vazhnov/HydraMeter_0.4/MMTR_AFE_00_04_TORELEASE/Schematic_PDF_and_Pics/Ohm_AFE.png

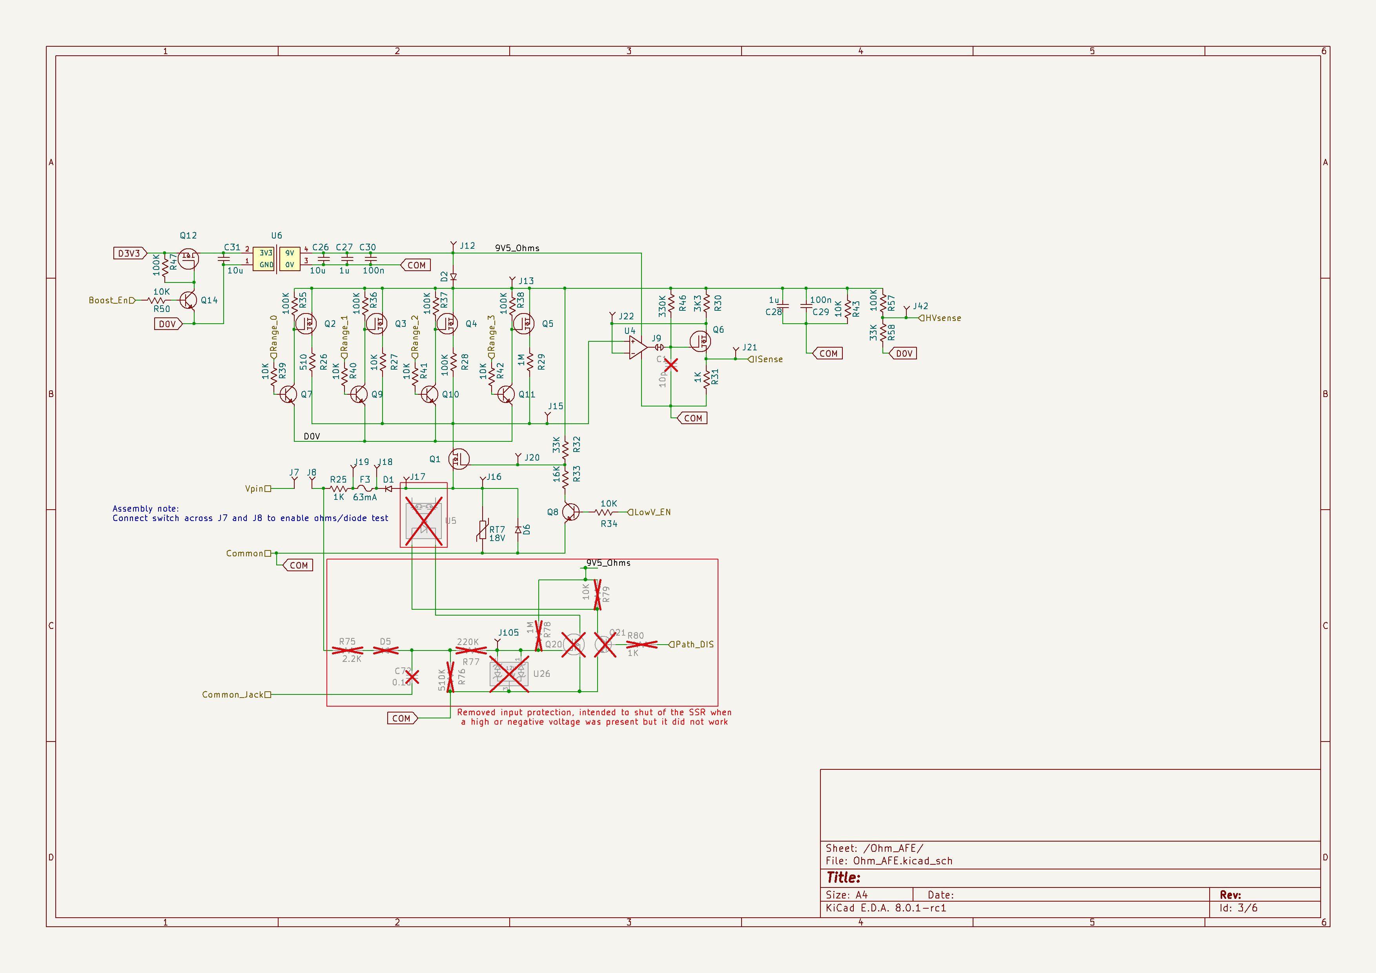
MMTR_AFE_00_04_TORELEASE/Schematic_PDF_and_Pics/Ohm_AFE.png
