vazhnov/HydraMeter_0.4/MMTR_AFE_00_04_TORELEASE/Schematic_PDF_and_Pics/PGA_ADC.png

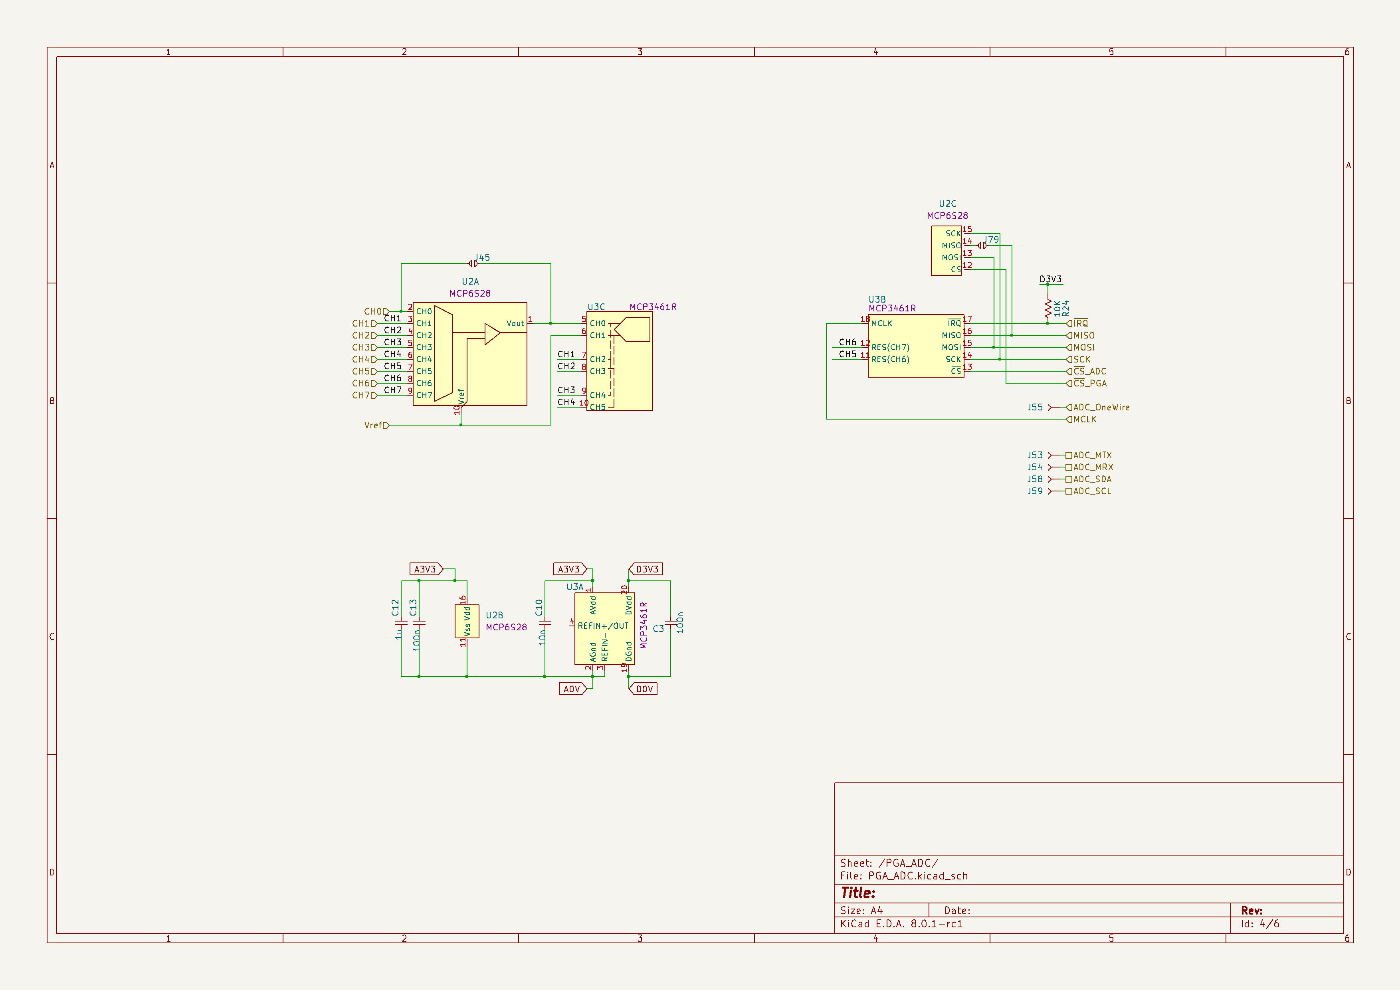
MMTR_AFE_00_04_TORELEASE/Schematic_PDF_and_Pics/PGA_ADC.png
