vazhnov/HydraMeter_0.4/MMTR_V00_03_Case/raspberry-pi-pico-r3-1.snapshot.2/SMD Resistor, Configurable, Raspberry Pi Pico-R3.SLDPRT

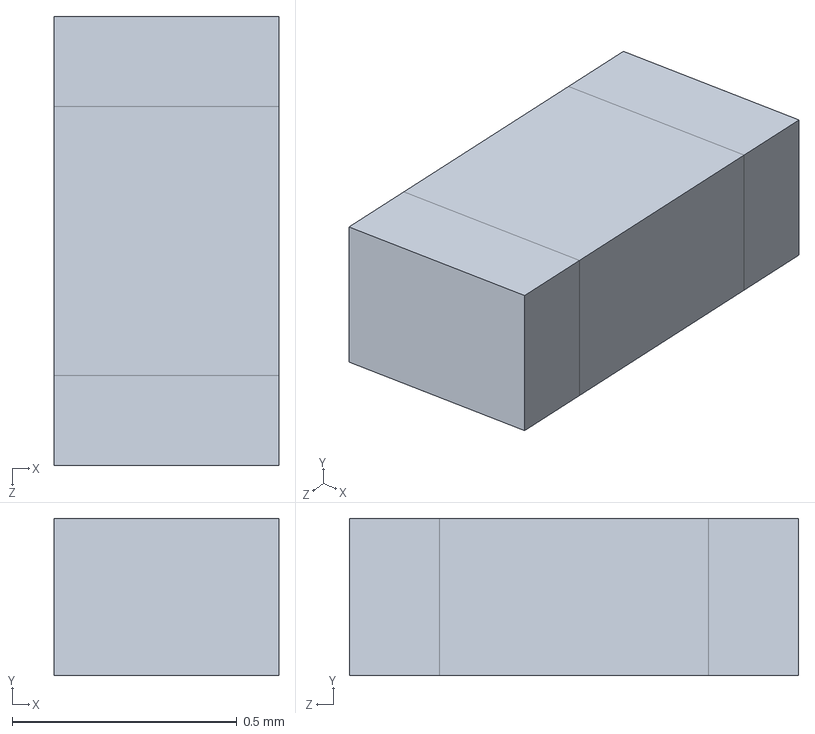
[picture p21: CAD file, 2024-12-21]
MMTR_V00_03_Case/raspberry-pi-pico-r3-1.snapshot.2/SMD Resistor, Configurable, Raspberry Pi Pico-R3.SLDPRT
0.5 x 0.35 x 1.00 mm
