vazhnov/HydraMeter_0.4/MMTR_V00_03_Case/raspberry-pi-pico-r3-1.snapshot.2/MicroUSB Port, Raspberry Pi Pico-R3.SLDPRT

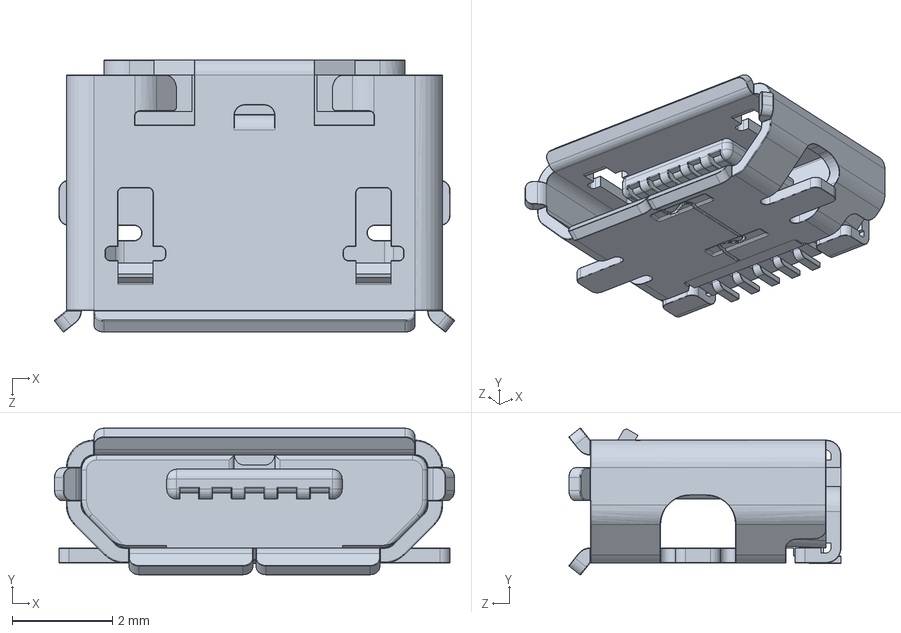
[picture p22: CAD file, 2024-12-21]
MMTR_V00_03_Case/raspberry-pi-pico-r3-1.snapshot.2/MicroUSB Port, Raspberry Pi Pico-R3.SLDPRT
7.97 x 2.92 x 5.43 mm
