vazhnov/HydraMeter_0.4/MMTR_V00_03_Case/raspberry-pi-pico-r3-1.snapshot.2/Q1, MOSFET, DMG1012T, Raspberry Pi Pico-R3.SLDPRT

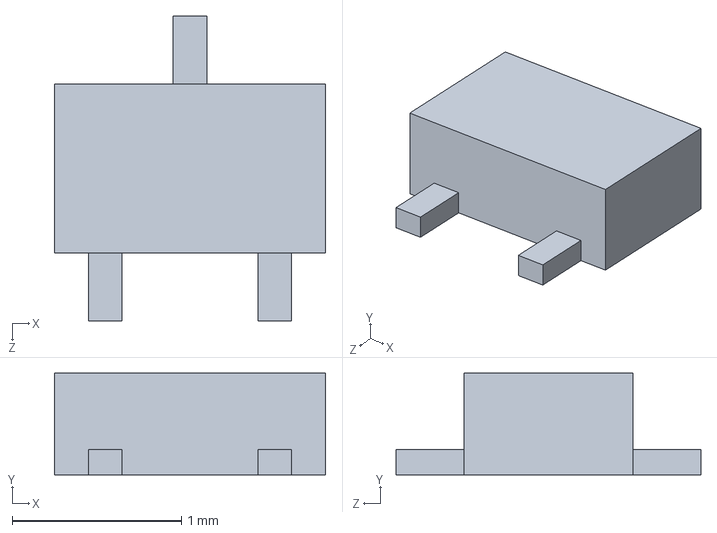
[picture p23: CAD file, 2024-12-21]
MMTR_V00_03_Case/raspberry-pi-pico-r3-1.snapshot.2/Q1, MOSFET, DMG1012T, Raspberry Pi Pico-R3.SLDPRT
1.60 x 0.6 x 1.80 mm
