vazhnov/HydraMeter_0.4/MMTR_V00_03_Case/raspberry-pi-pico-r3-1.snapshot.2/SW1, Tact Switch, Raspberry Pi Pico-R3.SLDPRT

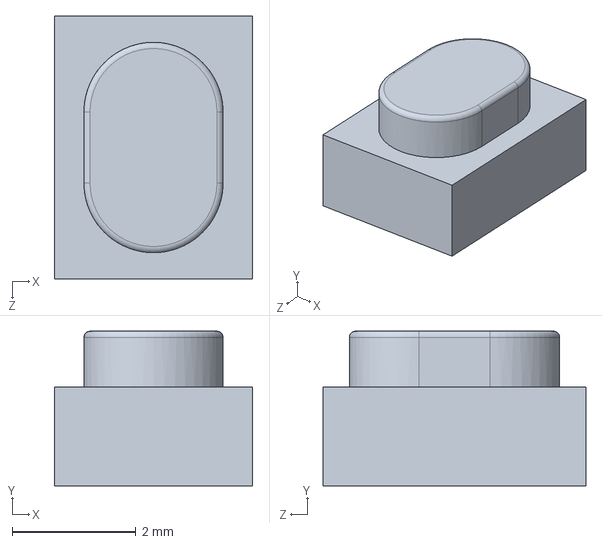
[picture p24: CAD file, 2024-12-21]
MMTR_V00_03_Case/raspberry-pi-pico-r3-1.snapshot.2/SW1, Tact Switch, Raspberry Pi Pico-R3.SLDPRT
3.20 x 2.50 x 4.25 mm
