vazhnov/HydraMeter_0.4/MMTR_V00_03_Case/raspberry-pi-pico-r3-1.snapshot.2/D2, QSME-C194, LED, Raspberry Pi Pico-R3.SLDPRT

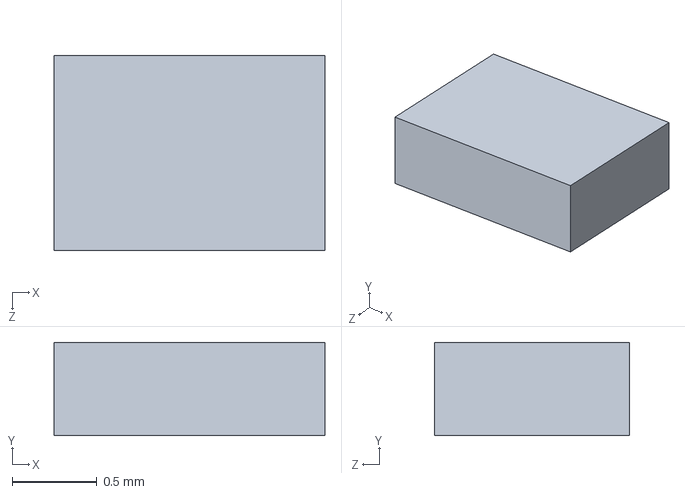
[picture p25: CAD file, 2024-12-21]
MMTR_V00_03_Case/raspberry-pi-pico-r3-1.snapshot.2/D2, QSME-C194, LED, Raspberry Pi Pico-R3.SLDPRT
1.60 x 0.55 x 1.15 mm
