vazhnov/HydraMeter_0.4/MMTR_V00_03_Case/raspberry-pi-pico-r3-1.snapshot.2/L1, Inductor, Raspberry Pi Pico-R3.SLDPRT

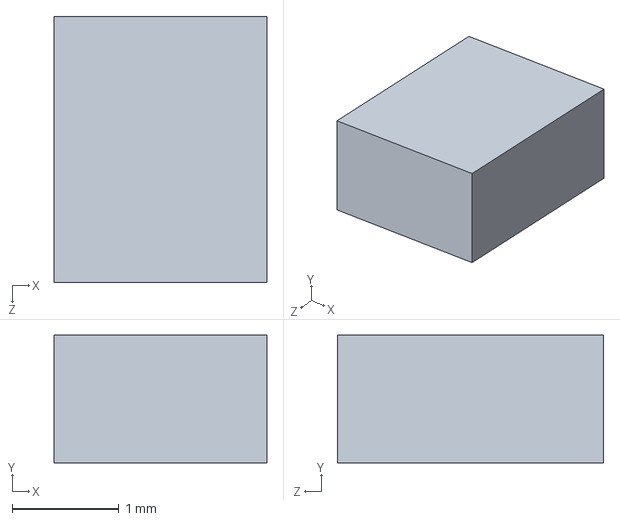
[picture p26: CAD file, 2024-12-21]
MMTR_V00_03_Case/raspberry-pi-pico-r3-1.snapshot.2/L1, Inductor, Raspberry Pi Pico-R3.SLDPRT
2.00 x 1.20 x 2.50 mm
