vazhnov/HydraMeter_0.4/Code/Display_VP_10_WirelessV2_SC/16ptFont_16_22_5_57.h

#ifndef FONT16_H
#define FONT16_H
uint8_t fontAsciiOffset_16 = 32;
uint8_t fontHtBytes_16 = 2;
uint8_t fontMaxWid_16 = 17;
int fontNumChars_16 = 98;
//uint8_t fontWidths[]
//int fontOffsets[]
uint8_t fontData_16[] = {
  0x00,0x00,0x00,0x00,0x00,0x00,0x00,0x00,   0x00,0x00,0x00,0x00,0x00,0x00,0x00,0x00,   // = 32 ==  
  0x00,0x00,0x7F,0x7F,0x00,0x00,   0x00,0x00,0xF3,0xF3,0x00,0x00,   // = 33 == !
  0x00,0x00,0x7C,0x7C,0x00,0x7C,0x7C,0x00,0x00,   0x00,0x00,0x00,0x00,0x00,0x00,0x00,0x00,0x00,   // = 34 == "
  0x00,0x00,0x06,0x06,0x07,0x7F,0x7E,0x06,0x06,0x07,0x7F,0x7E,0x06,0x06,   0x00,0x18,0x1B,0x7F,0xFC,0xD8,0x18,0x19,0x3F,0xFE,0xF8,0x18,0x18,0x00,   // = 35 == #
  0x00,0x1E,0x3F,0x33,0x61,0xFF,0xFF,0x70,0x3C,0x18,0x00,   0x00,0x0C,0x0E,0x87,0x83,0xFF,0xFF,0xE3,0x7F,0x3E,0x00,   // = 36 == $
  0x00,0x1F,0x3F,0x61,0x61,0x3F,0x3F,0x00,0x03,0x0F,0x3C,0x70,0x40,0x00,0x00,0x00,   0x00,0x00,0x80,0x80,0x83,0x8F,0x3C,0xF0,0xC0,0x3C,0x7E,0xC3,0xC3,0xC3,0x7E,0x3C,   // = 37 == %
  0x00,0x00,0x00,0x1E,0x3F,0x31,0x71,0x73,0x3F,0x3E,0x00,0x00,0x00,0x00,   0x00,0x3C,0x7E,0xE7,0xC3,0xE3,0xF3,0xBF,0x1E,0x1E,0x3F,0x73,0x01,0x00,   // = 38 == &
  0x00,0x00,0x7C,0x7C,0x00,0x00,   0x00,0x00,0x00,0x00,0x00,0x00,   // = 39 == '
  0x00,0x0F,0x3F,0xF0,0x80,0x80,   0x00,0xF0,0xFC,0x1E,0x03,0x00,   // = 40 == (
  0x00,0x80,0xC0,0xFC,0x3F,0x07,   0x00,0x01,0x03,0x3E,0xF8,0xE0,   // = 41 == )
  0x00,0x18,0x1A,0x7E,0x7C,0x1E,0x1A,0x00,   0x00,0x00,0x00,0x00,0x00,0x00,0x00,0x00,   // = 42 == *
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
  10, // 48 == 0
  10, // 49 == 1
  10, // 50 == 2
  10, // 51 == 3
  10, // 52 == 4
  10, // 53 == 5
  10, // 54 == 6
  10, // 55 == 7
  10, // 56 == 8
  10, // 57 == 9
  6, // 58 == :
  6, // 59 == ;
  10, // 60 == <
  10, // 61 == =
  10, // 62 == >
  11, // 63 == ?
  14, // 64 == @
  10, // 65 == A
  11, // 66 == B
  11, // 67 == C
  11, // 68 == D
  10, // 69 == E
  10, // 70 == F
  11, // 71 == G
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
};
#endif
