vazhnov/HydraMeter_0.4/Code/Display_VP_10_WirelessV2_SC/24ptFont_16_20_30_5.h

#ifndef FONT24_H
#define FONT24_H
uint8_t fontAsciiOffset_24 = 32;
uint8_t fontHtBytes_24 = 3;
uint8_t fontMaxWid_24 = 21;
int fontNumChars_24 = 98;
//uint8_t fontWidths[]
//int fontOffsets[]
uint8_t fontData_24[] = {
  0x00,0x00,0x00,0x00,0x00,0x00,0x00,0x00,   0x00,0x00,0x00,0x00,0x00,0x00,0x00,0x00,   0x00,0x00,0x00,0x00,0x00,0x00,0x00,0x00,   // = 32 ==  
  0x00,0x00,0x1F,0x1F,0x1F,0x00,   0x00,0x00,0xFF,0xFF,0xFF,0x00,   0x00,0x00,0xC7,0xC7,0x07,0x00,   // = 33 == !
  0x00,0x1C,0x1F,0x1F,0x10,0x00,0x1F,0x1F,0x1E,0x00,   0x00,0x00,0xC0,0xC0,0x00,0x00,0xC0,0xC0,0x00,0x00,   0x00,0x00,0x00,0x00,0x00,0x00,0x00,0x00,0x00,0x00,   // = 34 == "
  0x00,0x00,0x00,0x1F,0x1F,0x1F,0x00,0x00,0x1F,0x1F,0x1E,0x00,   0x00,0xC0,0xC7,0xFF,0xFF,0xC0,0xC0,0xFF,0xFF,0xFF,0xC0,0xC0,   0x40,0xC3,0xFF,0xFF,0xE0,0xC0,0xCF,0xFF,0xFF,0xC0,0xC0,0x00,   // = 35 == #
  0x00,0x01,0x07,0x0F,0x0F,0x3E,0x3E,0x0F,0x0F,0x07,0x01,0x00,   0x00,0xE0,0xF8,0xFC,0x7E,0x1E,0x0F,0x07,0xC3,0xC1,0xC0,0x00,   0x00,0x38,0x3E,0x3F,0x0F,0x07,0x07,0xCF,0xFF,0xFE,0x78,0x00,   // = 36 == $
  0x00,0x0F,0x1F,0x18,0x18,0x1F,0x0F,0x00,0x00,0x00,0x03,0x0F,0x1E,0x10,0x00,0x00,0x00,0x00,   0x00,0xFC,0xFC,0x06,0x06,0xFE,0xFC,0x03,0x0F,0x7E,0xF3,0x87,0x0E,0x0C,0x0E,0x07,0x03,0x00,   0x00,0x00,0x00,0x00,0x03,0x1F,0x7C,0xF0,0x80,0x00,0xFC,0xFF,0x03,0x03,0x07,0xFE,0xFC,0x00,   // = 37 == %
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
  12, // 50 == 2
  12, // 51 == 3
  12, // 52 == 4
  12, // 53 == 5
  12, // 54 == 6
  12, // 55 == 7
  12, // 56 == 8
  12, // 57 == 9
  6, // 58 == :
  6, // 59 == ;
  12, // 60 == <
  12, // 61 == =
  12, // 62 == >
  11, // 63 == ?
  21, // 64 == @
  12, // 65 == A
  12, // 66 == B
  11, // 67 == C
  12, // 68 == D
  11, // 69 == E
  10, // 70 == F
  12, // 71 == G
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
};
#endif
