vazhnov/HydraMeter_0.4/Code/Display_VP_10_WirelessV2_SC/48ptFont_23_8_58_20.h

#ifndef FONT48_H
#define FONT48_H
uint8_t fontAsciiOffset_48 = 32;
uint8_t fontHtBytes_48 = 6;
uint8_t fontMaxWid_48 = 29;
int fontNumChars_48 = 94;
//uint8_t fontWidths[]
//int fontOffsets[]
uint8_t fontData_48[] = {
  0x00,0x00,0x00,0x00,0x00,0x00,0x00,0x00,0x00,0x00,   0x00,0x00,0x00,0x00,0x00,0x00,0x00,0x00,0x00,0x00,   0x00,0x00,0x00,0x00,0x00,0x00,0x00,0x00,0x00,0x00,   0x00,0x00,0x00,0x00,0x00,0x00,0x00,0x00,0x00,0x00,   0x00,0x00,0x00,0x00,0x00,0x00,0x00,0x00,0x00,0x00,   0x00,0x00,0x00,0x00,0x00,0x00,0x00,0x00,0x00,0x00,   // = 32 ==  
  0x00,0x00,0x7F,0x7F,0x7F,0x7F,0x7F,0x00,0x00,   0x00,0x00,0xFF,0xFF,0xFF,0xFF,0xFF,0x00,0x00,   0x00,0x00,0xFF,0xFF,0xFF,0xFF,0xFF,0x00,0x00,   0x00,0x00,0x80,0xFF,0xFF,0xFF,0xFF,0x00,0x00,   0x00,0x00,0x00,0xFC,0xFC,0xFC,0x80,0x00,0x00,   0x00,0x00,0x7E,0x7E,0x7E,0x7E,0x7E,0x00,0x00,   // = 33 == !
  0x00,0x00,0x7F,0x7F,0x7F,0x7F,0x00,0x00,0x00,0x7F,0x7F,0x7F,0x7F,0x00,   0x00,0x00,0xF8,0xFC,0xFC,0xF0,0x00,0x00,0x00,0xF8,0xFC,0xFC,0xF0,0x00,   0x00,0x00,0x00,0x00,0x00,0x00,0x00,0x00,0x00,0x00,0x00,0x00,0x00,0x00,   0x00,0x00,0x00,0x00,0x00,0x00,0x00,0x00,0x00,0x00,0x00,0x00,0x00,0x00,   0x00,0x00,0x00,0x00,0x00,0x00,0x00,0x00,0x00,0x00,0x00,0x00,0x00,0x00,   0x00,0x00,0x00,0x00,0x00,0x00,0x00,0x00,0x00,0x00,0x00,0x00,0x00,0x00,   // = 34 == "
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
0, // 32
60, // 33
114, // 34
198, // 35
330, // 36
426, // 37
588, // 38
714, // 39
756, // 40
840, // 41
924, // 42
1038, // 43
1194, // 44
1242, // 45
1302, // 46
1344, // 47
1428, // 48
1536, // 49
1644, // 50
1752, // 51
1860, // 52
1968, // 53
2076, // 54
2184, // 55
2292, // 56
2400, // 57
2508, // 58
2550, // 59
2598, // 60
2754, // 61
2910, // 62
3066, // 63
3168, // 64
3342, // 65
3456, // 66
3564, // 67
3666, // 68
3774, // 69
3870, // 70
3960, // 71
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
};
uint8_t fontWidths_48[] = {
  10, // 32 ==  
  9, // 33 == !
  14, // 34 == "
  22, // 35 == #
  16, // 36 == $
  27, // 37 == %
  21, // 38 == &
  7, // 39 == '
  14, // 40 == (
  14, // 41 == )
  19, // 42 == *
  26, // 43 == +
  8, // 44 == ,
  10, // 45 == -
  7, // 46 == .
  14, // 47 == /
  18, // 48 == 0
  18, // 49 == 1
  18, // 50 == 2
  18, // 51 == 3
  18, // 52 == 4
  18, // 53 == 5
  18, // 54 == 6
  18, // 55 == 7
  18, // 56 == 8
  18, // 57 == 9
  7, // 58 == :
  8, // 59 == ;
  26, // 60 == <
  26, // 61 == =
  26, // 62 == >
  17, // 63 == ?
  29, // 64 == @
  19, // 65 == A
  18, // 66 == B
  17, // 67 == C
  18, // 68 == D
  16, // 69 == E
  15, // 70 == F
  18, // 71 == G
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
};
#endif
