vazhnov/HydraMeter_0.4/Code/Display_VP_10_WirelessV2_SC/8ptFont_5_23_40_23.h

#ifndef FONT8_H
#define FONT8_H
uint8_t fontAsciiOffset_8 = 32;
uint8_t fontHtBytes_8 = 1;
uint8_t fontMaxWid_8 = 6;
int fontNumChars_8 = 90;
//uint8_t fontWidths[]
//int fontOffsets[]
uint8_t fontData_8[] = {
  0x00,0x00,0x00,0x00,0x00,   // = 32 ==  
  0xFD,0x00,   // = 33 == !
  0xC0,0x00,0xC0,0x00,   // = 34 == "
     // = 35 == #
  0x22,0x53,0xD2,0x4C,0x00,   // = 36 == $
     // = 37 == %
     // = 38 == &
  0xC0,0x00,   // = 39 == '
  0x7E,0x81,0x00,   // = 40 == (
  0x81,0x7E,0x00,   // = 41 == )
     // = 42 == *
     // = 43 == +
  0x03,0x00,   // = 44 == ,
  0x10,0x10,0x10,0x10,0x00,   // = 45 == -
  0x03,0x03,0x00,   // = 46 == .
     // = 47 == /
  0x7E,0x89,0x91,0x7E,0x00,   // = 48 == 0
  0x00,0x40,0xFF,0x00,0x00,   // = 49 == 1
  0x8F,0x91,0x91,0x61,0x00,   // = 50 == 2
  0x81,0x81,0x91,0x6E,0x00,   // = 51 == 3
  0xF0,0x10,0x10,0xFF,0x00,   // = 52 == 4
  0xE1,0x91,0x91,0x8E,0x00,   // = 53 == 5
  0x7E,0x91,0x91,0x0E,0x00,   // = 54 == 6
  0x80,0x87,0x98,0xE0,0x00,   // = 55 == 7
  0x6E,0x91,0x91,0x6E,0x00,   // = 56 == 8
  0x70,0x89,0x89,0x7E,0x00,   // = 57 == 9
  0x22,0x00,   // = 58 == :
  0x23,0x00,   // = 59 == ;
     // = 60 == <
     // = 61 == =
     // = 62 == >
  0x80,0x8D,0x90,0x60,0x00,   // = 63 == ?
     // = 64 == @
  0x7F,0x88,0x88,0x7F,0x00,   // = 65 == A
  0xFF,0x91,0x91,0x6E,0x00,   // = 66 == B
  0x7E,0x81,0x81,0x81,0x00,   // = 67 == C
  0xFF,0x81,0x81,0x7E,0x00,   // = 68 == D
  0xFF,0x91,0x91,0x81,0x00,   // = 69 == E
  0xFF,0x90,0x90,0x80,0x00,   // = 70 == F
  0x7E,0x81,0x89,0x4E,0x00,   // = 71 == G
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
};
int fontOffsets_8[]={
0, // 32
5, // 33
7, // 34
11, // 35
11, // 36
16, // 37
16, // 38
16, // 39
18, // 40
21, // 41
24, // 42
24, // 43
24, // 44
26, // 45
31, // 46
34, // 47
34, // 48
39, // 49
44, // 50
49, // 51
54, // 52
59, // 53
64, // 54
69, // 55
74, // 56
79, // 57
84, // 58
86, // 59
88, // 60
88, // 61
88, // 62
88, // 63
93, // 64
93, // 65
98, // 66
103, // 67
108, // 68
113, // 69
118, // 70
123, // 71
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
};
uint8_t fontWidths_8[] = {
  5, // 32 ==  
  2, // 33 == !
  4, // 34 == "
  0, // 35 == #
  5, // 36 == $
  0, // 37 == %
  0, // 38 == &
  2, // 39 == '
  3, // 40 == (
  3, // 41 == )
  0, // 42 == *
  0, // 43 == +
  2, // 44 == ,
  5, // 45 == -
  3, // 46 == .
  0, // 47 == /
  5, // 48 == 0
  5, // 49 == 1
  5, // 50 == 2
  5, // 51 == 3
  5, // 52 == 4
  5, // 53 == 5
  5, // 54 == 6
  5, // 55 == 7
  5, // 56 == 8
  5, // 57 == 9
  2, // 58 == :
  2, // 59 == ;
  0, // 60 == <
  0, // 61 == =
  0, // 62 == >
  5, // 63 == ?
  0, // 64 == @
  5, // 65 == A
  5, // 66 == B
  5, // 67 == C
  5, // 68 == D
  5, // 69 == E
  5, // 70 == F
  5, // 71 == G
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
};
#endif
